Finomnis/busybeacon/.media/busybeacon_red_small.jpg

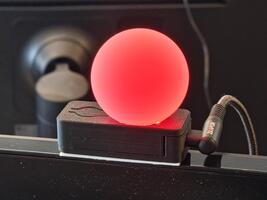
.media/busybeacon_red_small.jpg
