Finomnis/busybeacon/.media/busybeacon_yellow_small.jpg

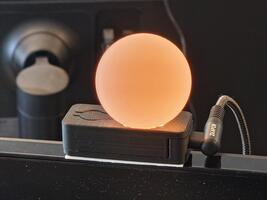
.media/busybeacon_yellow_small.jpg
